RivenHexagon/TAC_Scorpion/AML_LineIn/LineInMod.pdf

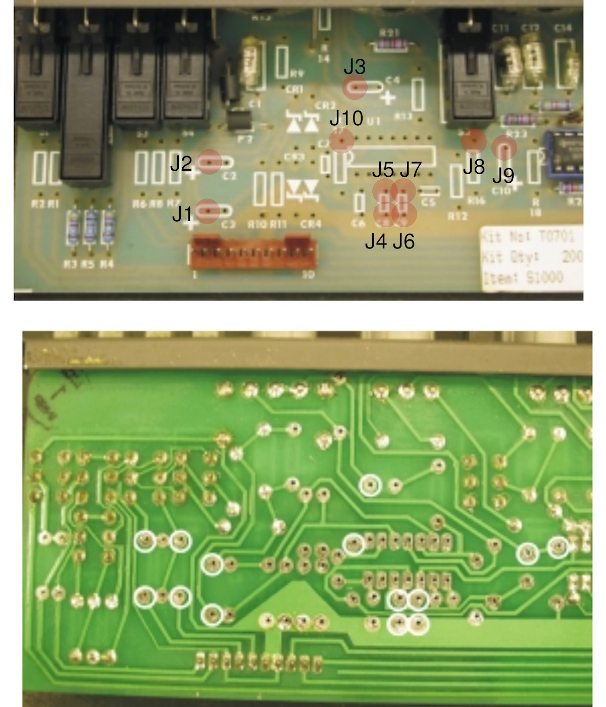
[picture p6: figure]
