RivenHexagon/TAC_Scorpion/AML_MicIn/MicInMod.pdf

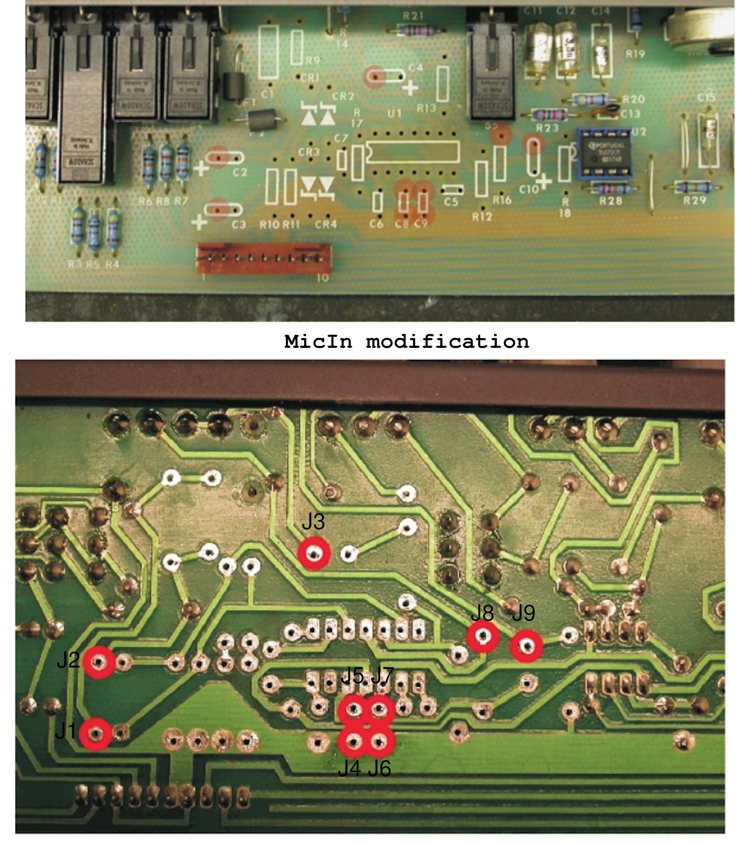
[picture p7: figure]
