RivenHexagon/TAC_Scorpion/AML_LineIn/AML-LineIn.jpg

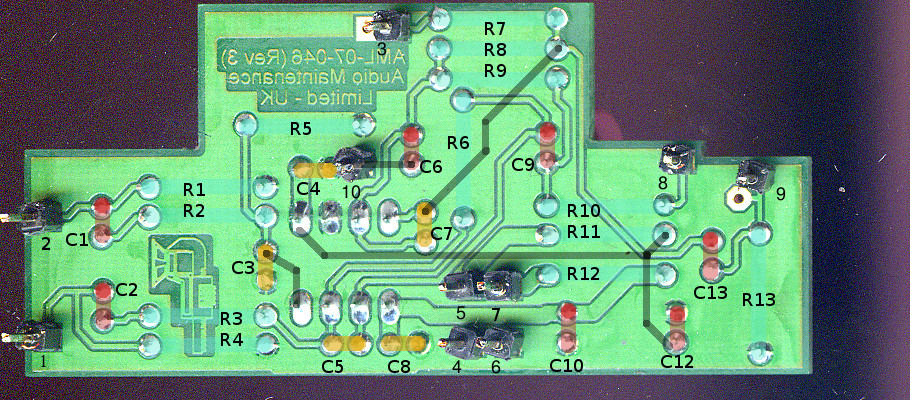
AML_LineIn/AML-LineIn.jpg
