RivenHexagon/TAC_Scorpion/DOA_SK25RHX/Docs/194913907.jpg

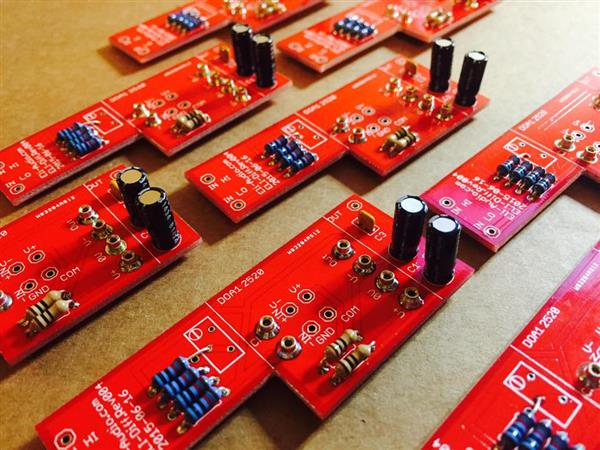
DOA_SK25RHX/Docs/194913907.jpg
