RivenHexagon/TAC_Scorpion/DOA_SK25RHX/Docs/194914601.jpg

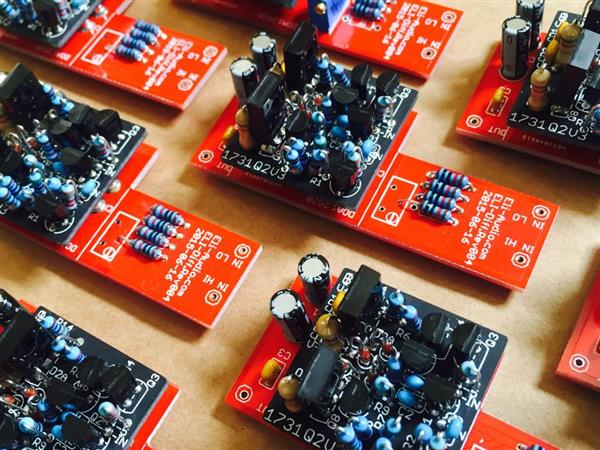
DOA_SK25RHX/Docs/194914601.jpg
