RivenHexagon/TAC_Scorpion/DOA_SK25RHX/Docs/194915174.jpg

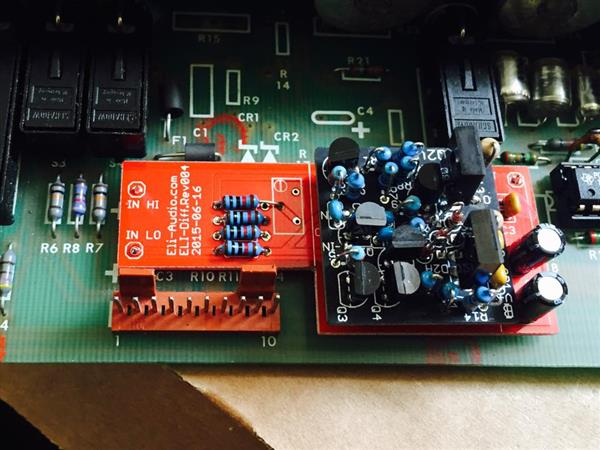
DOA_SK25RHX/Docs/194915174.jpg
