RivenHexagon/TAC_Scorpion/TAC_GL270D/GL270-DOA2520.kicad_pro/PCB_GL270D-flip.jpg

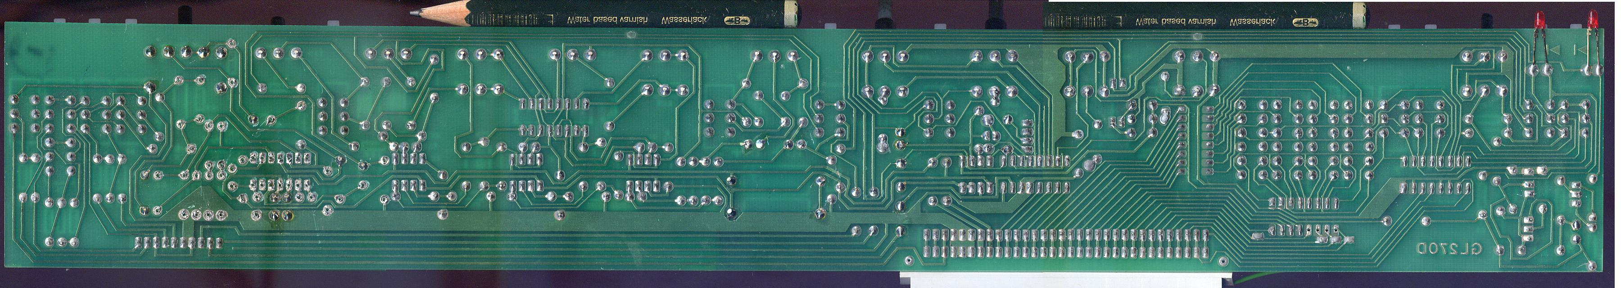
TAC_GL270D/GL270-DOA2520.kicad_pro/PCB_GL270D-flip.jpg
