RivenHexagon/TAC_Scorpion/DOA_SK25RHX/SK25.pdf

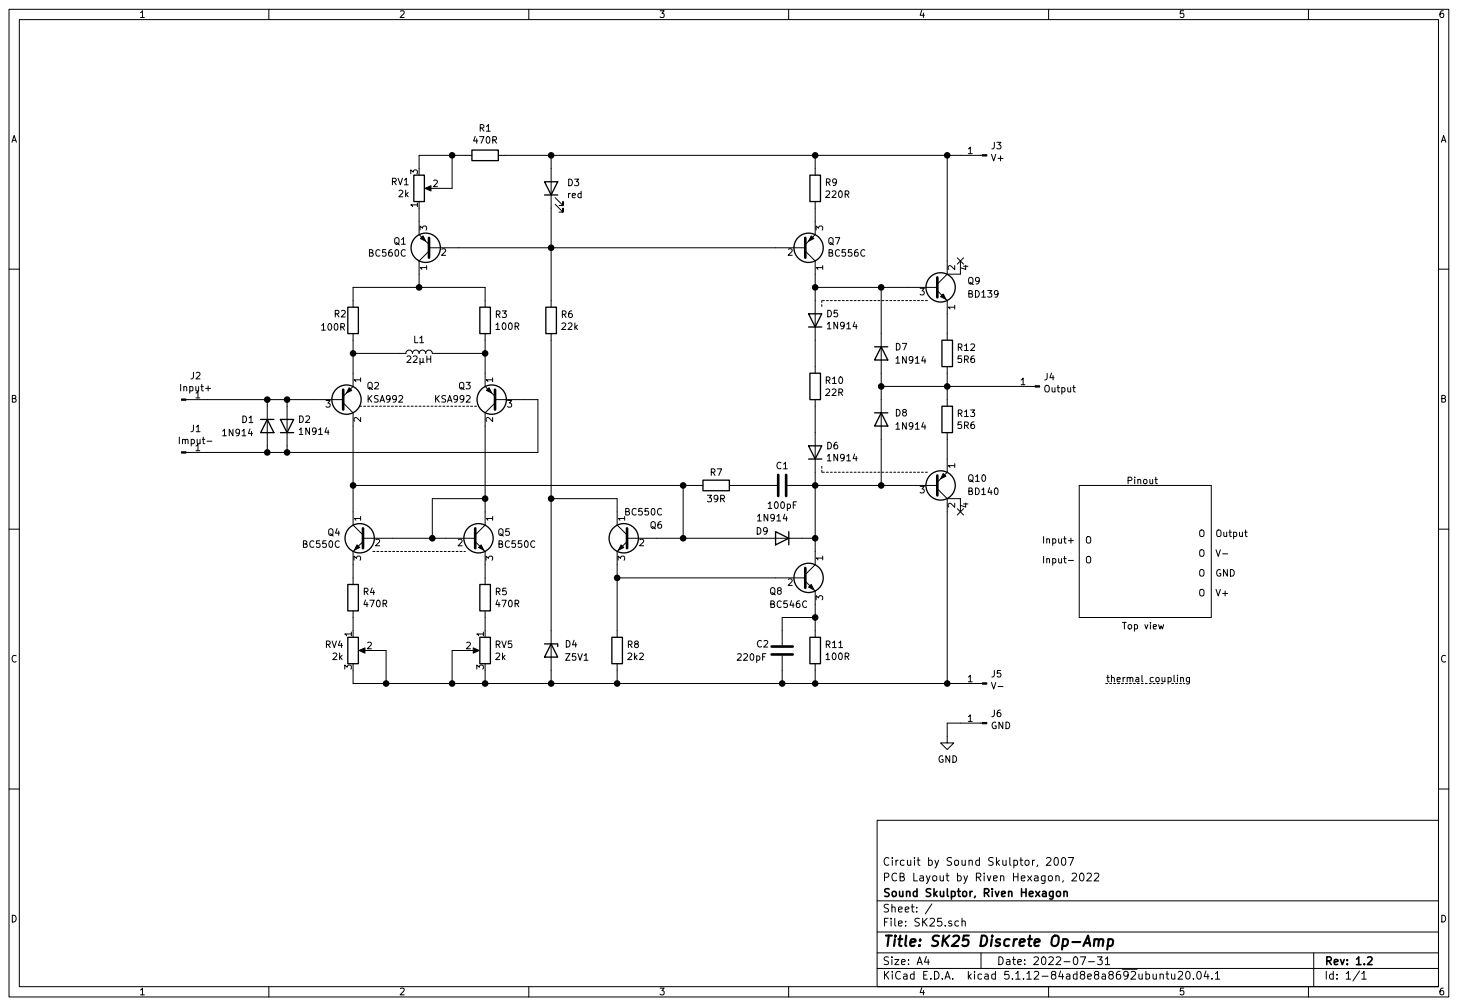
[picture p64: page 1]

Circuit by Sound Skulptor, 2007 D6

PCB Layout by Riven Hexagon, 2022
File: SK25.sch Sheet: / Sound Skulptor, Riven Hexagon

Id: 1/1 Title: SK25 Discrete Op-Amp
