RivenHexagon/TAC_Scorpion/TAC_GL270D/GL270-LineIn.pdf

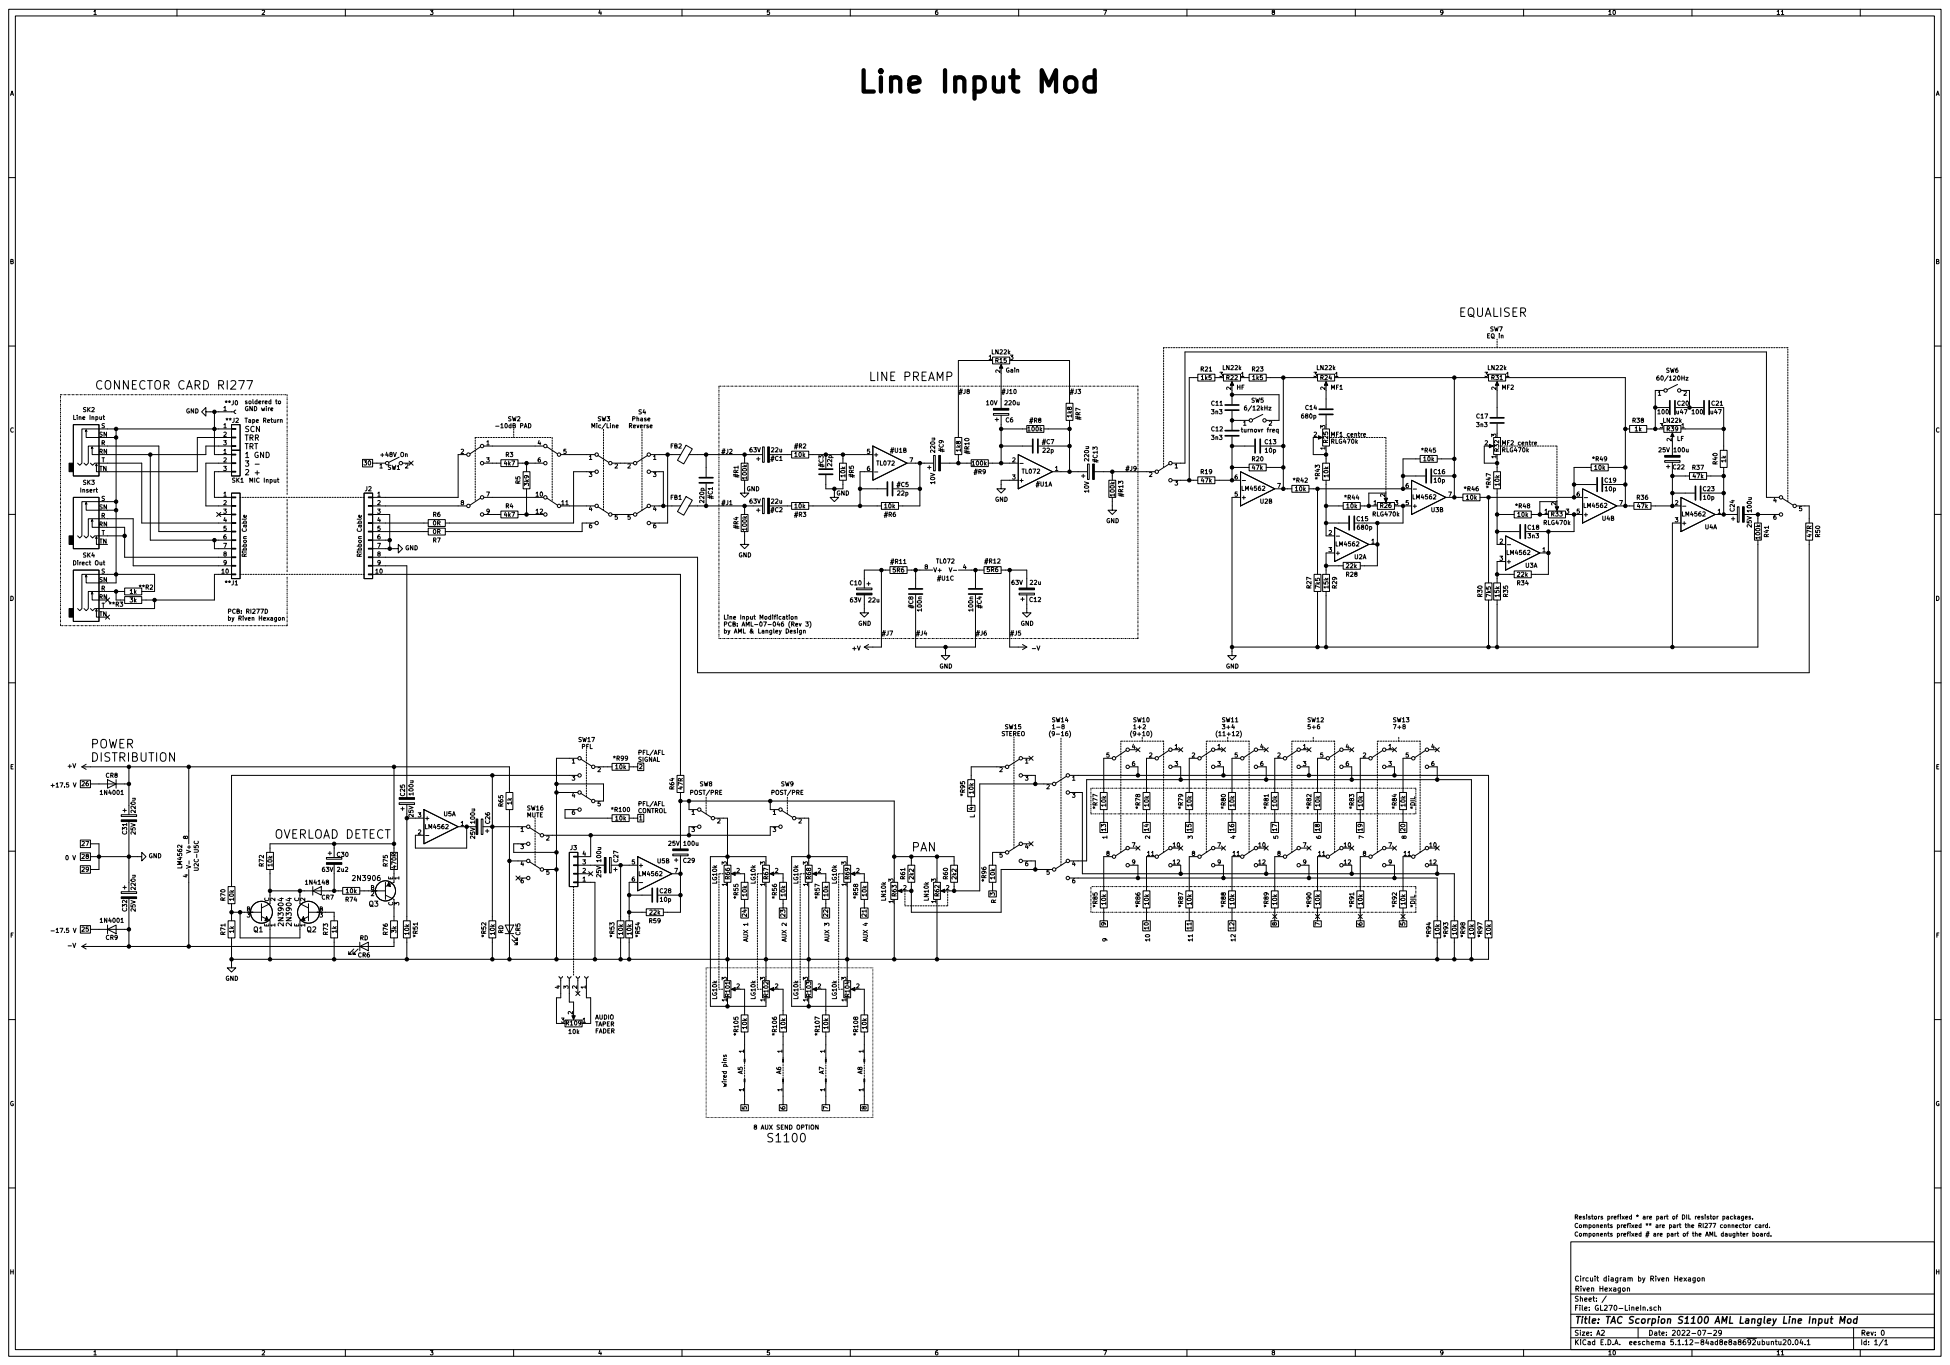
[picture p65: page 1]

Components prefixed ** are part the RI277 connector card. AUX 2

Resistors prefixed * are part of DIL resistor packages.

Circuit diagram by Riven Hexagon
File: GL270-LineIn.sch Sheet: / Riven Hexagon

Id: 1/1 Title: TAC Scorpion S1100 AML Langley Line Input Mod
