RivenHexagon/TAC_Scorpion/TAC_GL270D/GL270-MicIn.pdf

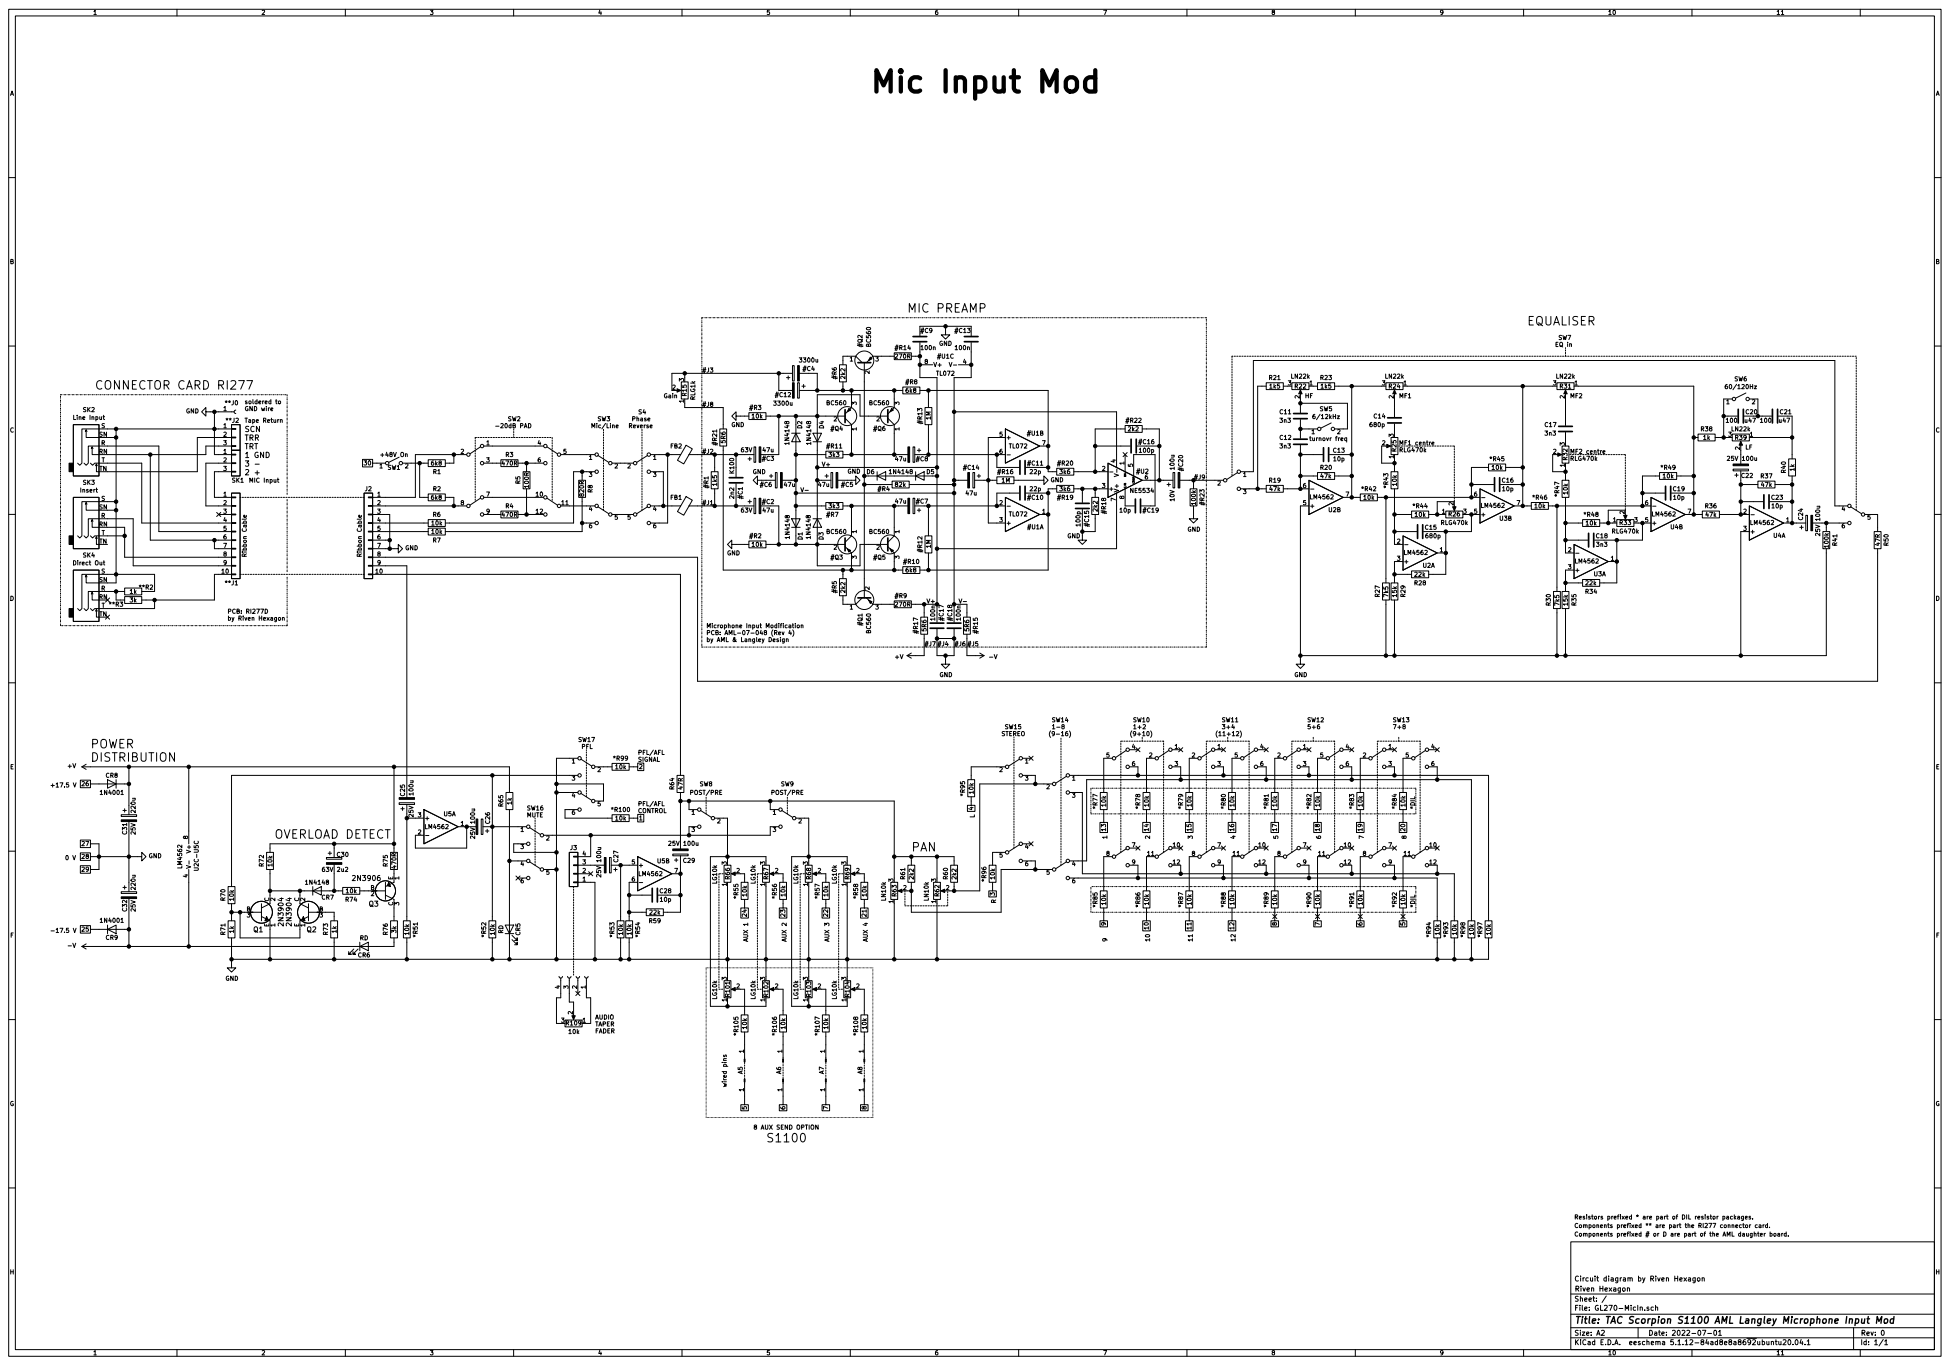
[picture p66: page 1]

soldered to GND wire +V

by AML & Langley Design AUX 2

Resistors prefixed * are part of DIL resistor packages.
Components prefixed ** are part the RI277 connector card.
Components prefixed # or D are part of the AML daughter board.

Circuit diagram by Riven Hexagon
File: GL270-MicIn.sch Sheet: / Riven Hexagon

Id: 1/1 Title: TAC Scorpion S1100 AML Langley Microphone Input Mod
