RivenHexagon/TAC_Scorpion/AML_LineIn/AML-07-046.pdf

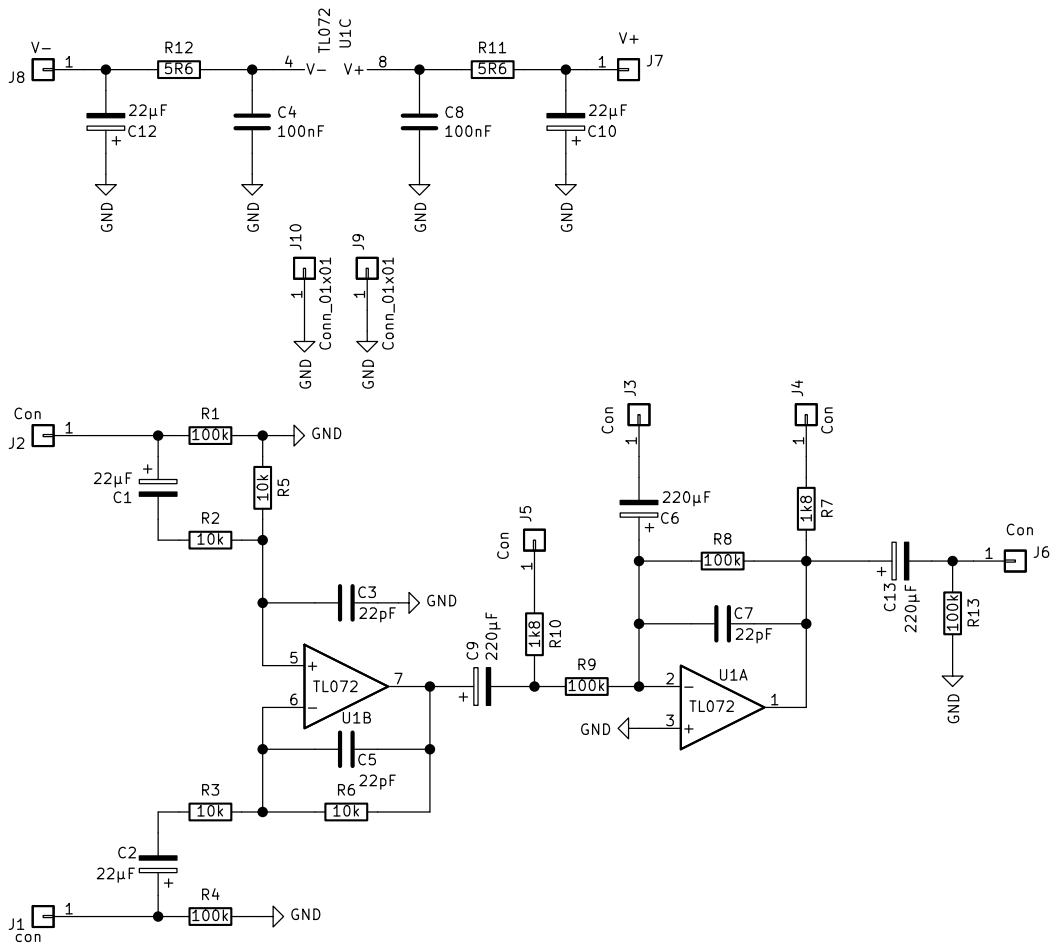
[picture p72: page 1]

Id: 1/1 Title: Scorpion Line Input File: AML-07-046.sch Sheet: /
