RivenHexagon/TAC_Scorpion/TAC_JP280/JP280C-B_Cu.pdf

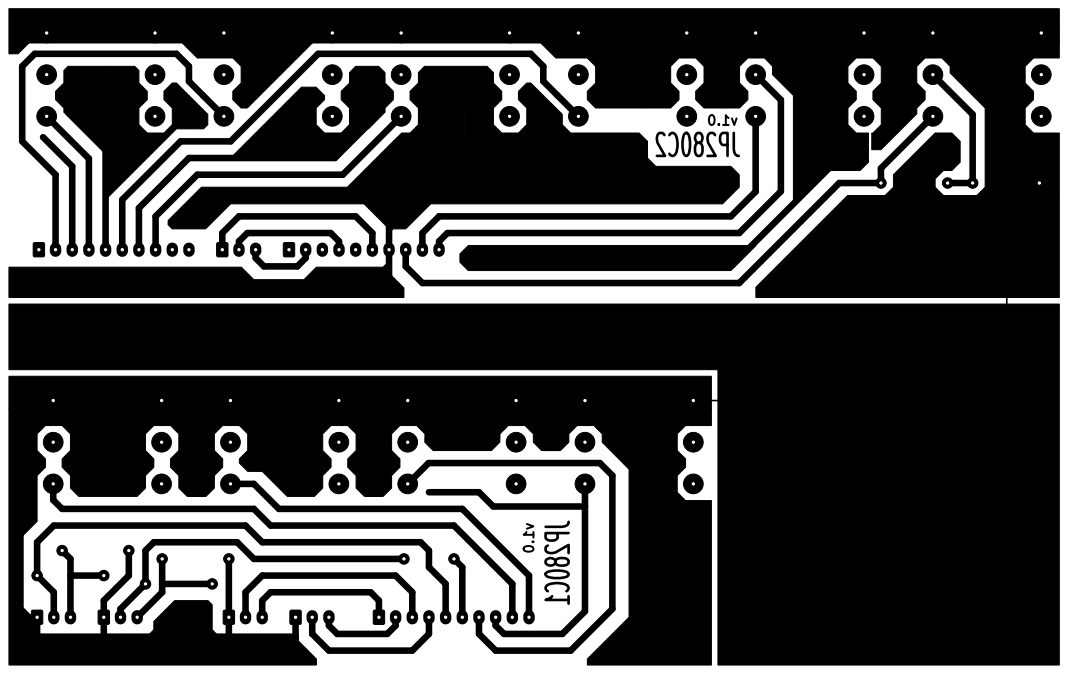
[picture p73: page 1]
