RivenHexagon/TAC_Scorpion/TAC_RI277/RI277D_v1.2.pdf

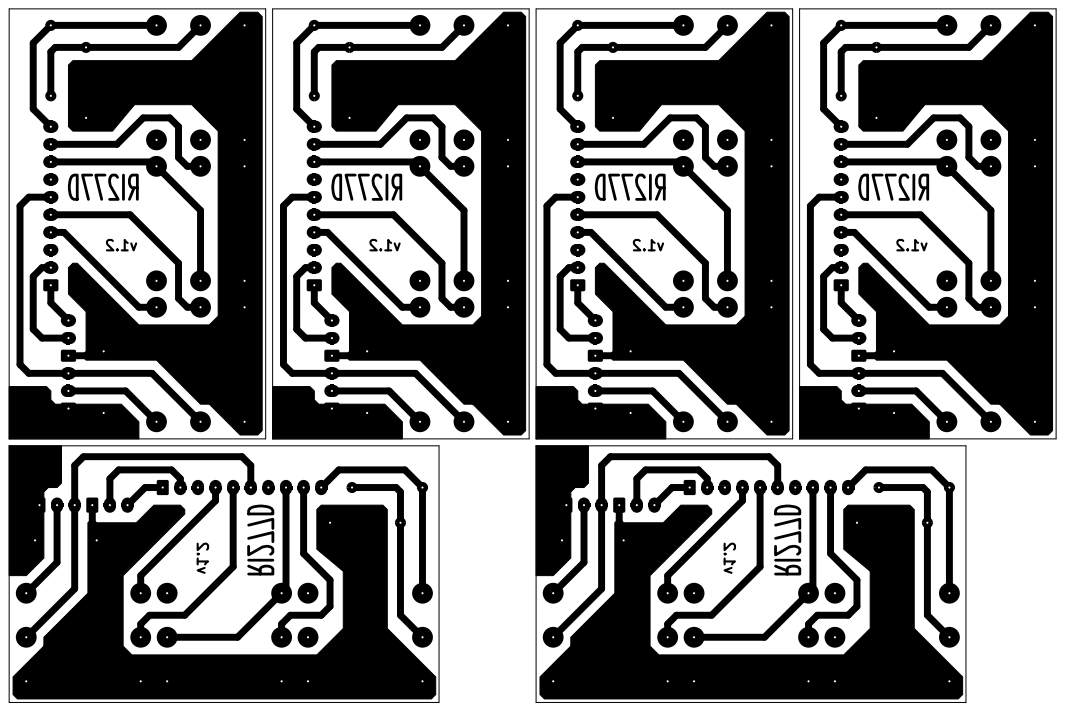
[picture p74: page 1]
