RivenHexagon/TAC_Scorpion/TAC_RI279/RI279C_v1.0.pdf

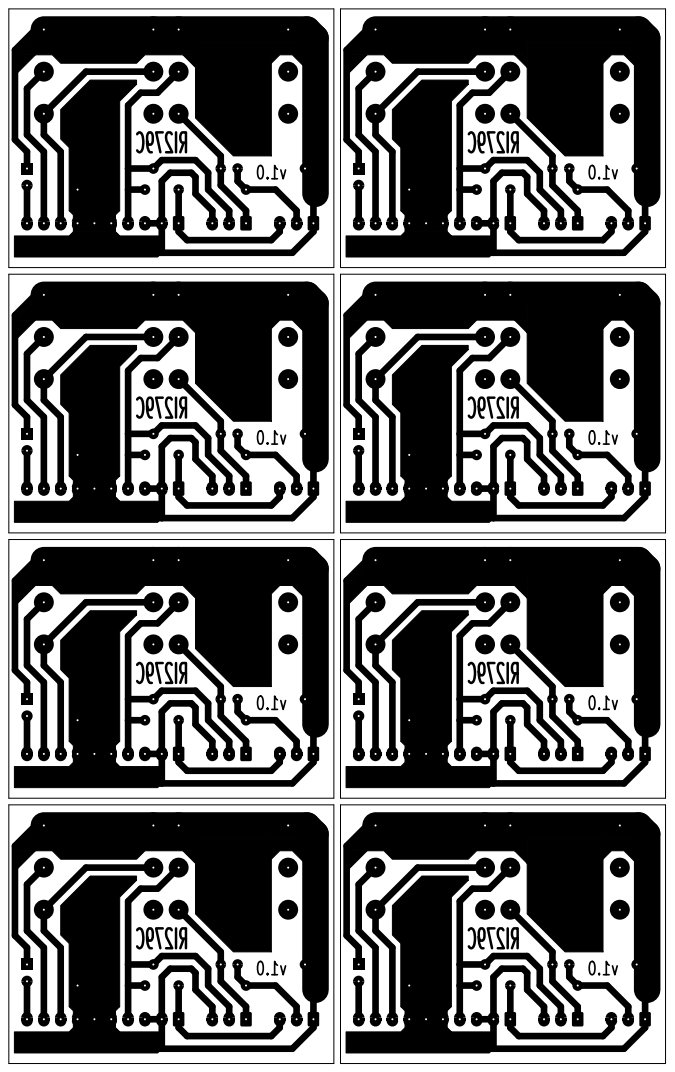
[picture p75: page 1]
