RivenHexagon/TAC_Scorpion/DOA_SK25RHX/Docs/sk25-layout-03.pdf

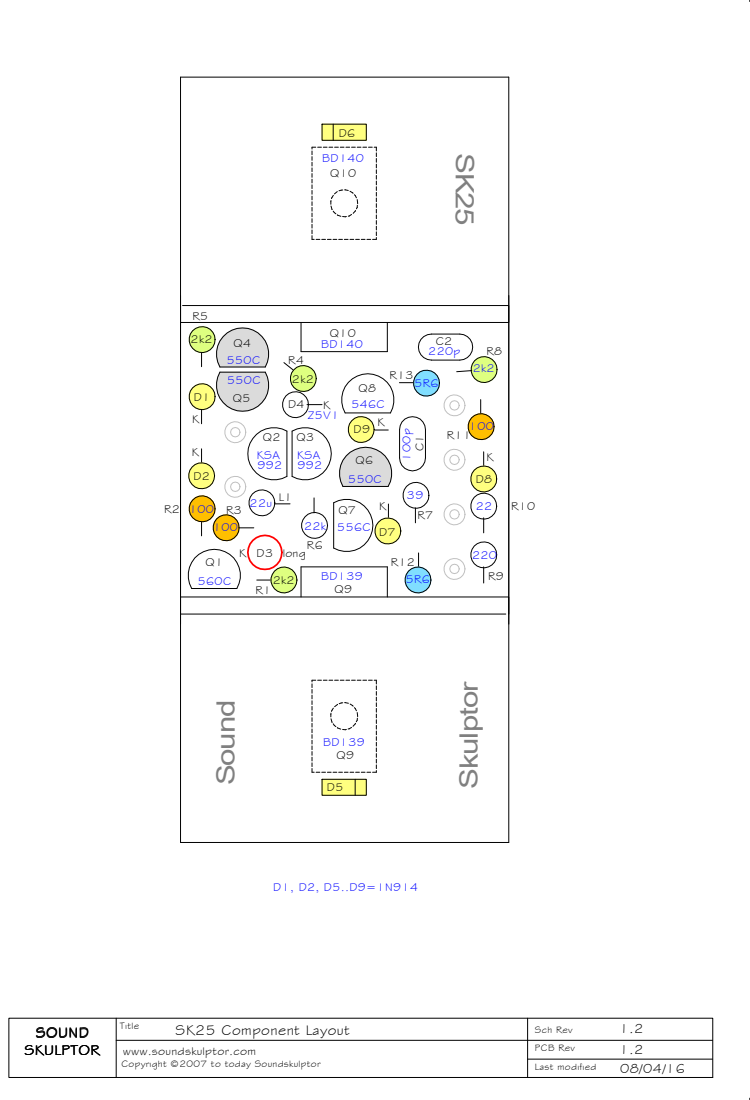
[picture p76: page 1]

www.soundskulptor.com
Copyright ©2007 to today Soundskulptor
