RivenHexagon/TAC_Scorpion/TAC_GL270D/GL270-DOA2520.kicad_pro/GL270-DOA2520.kicad_pro.kicad_sch

## KiCad design TAC_GL270D/GL270-DOA2520.kicad_pro/GL270-DOA2520.kicad_pro.kicad_sch (2023-12-30)

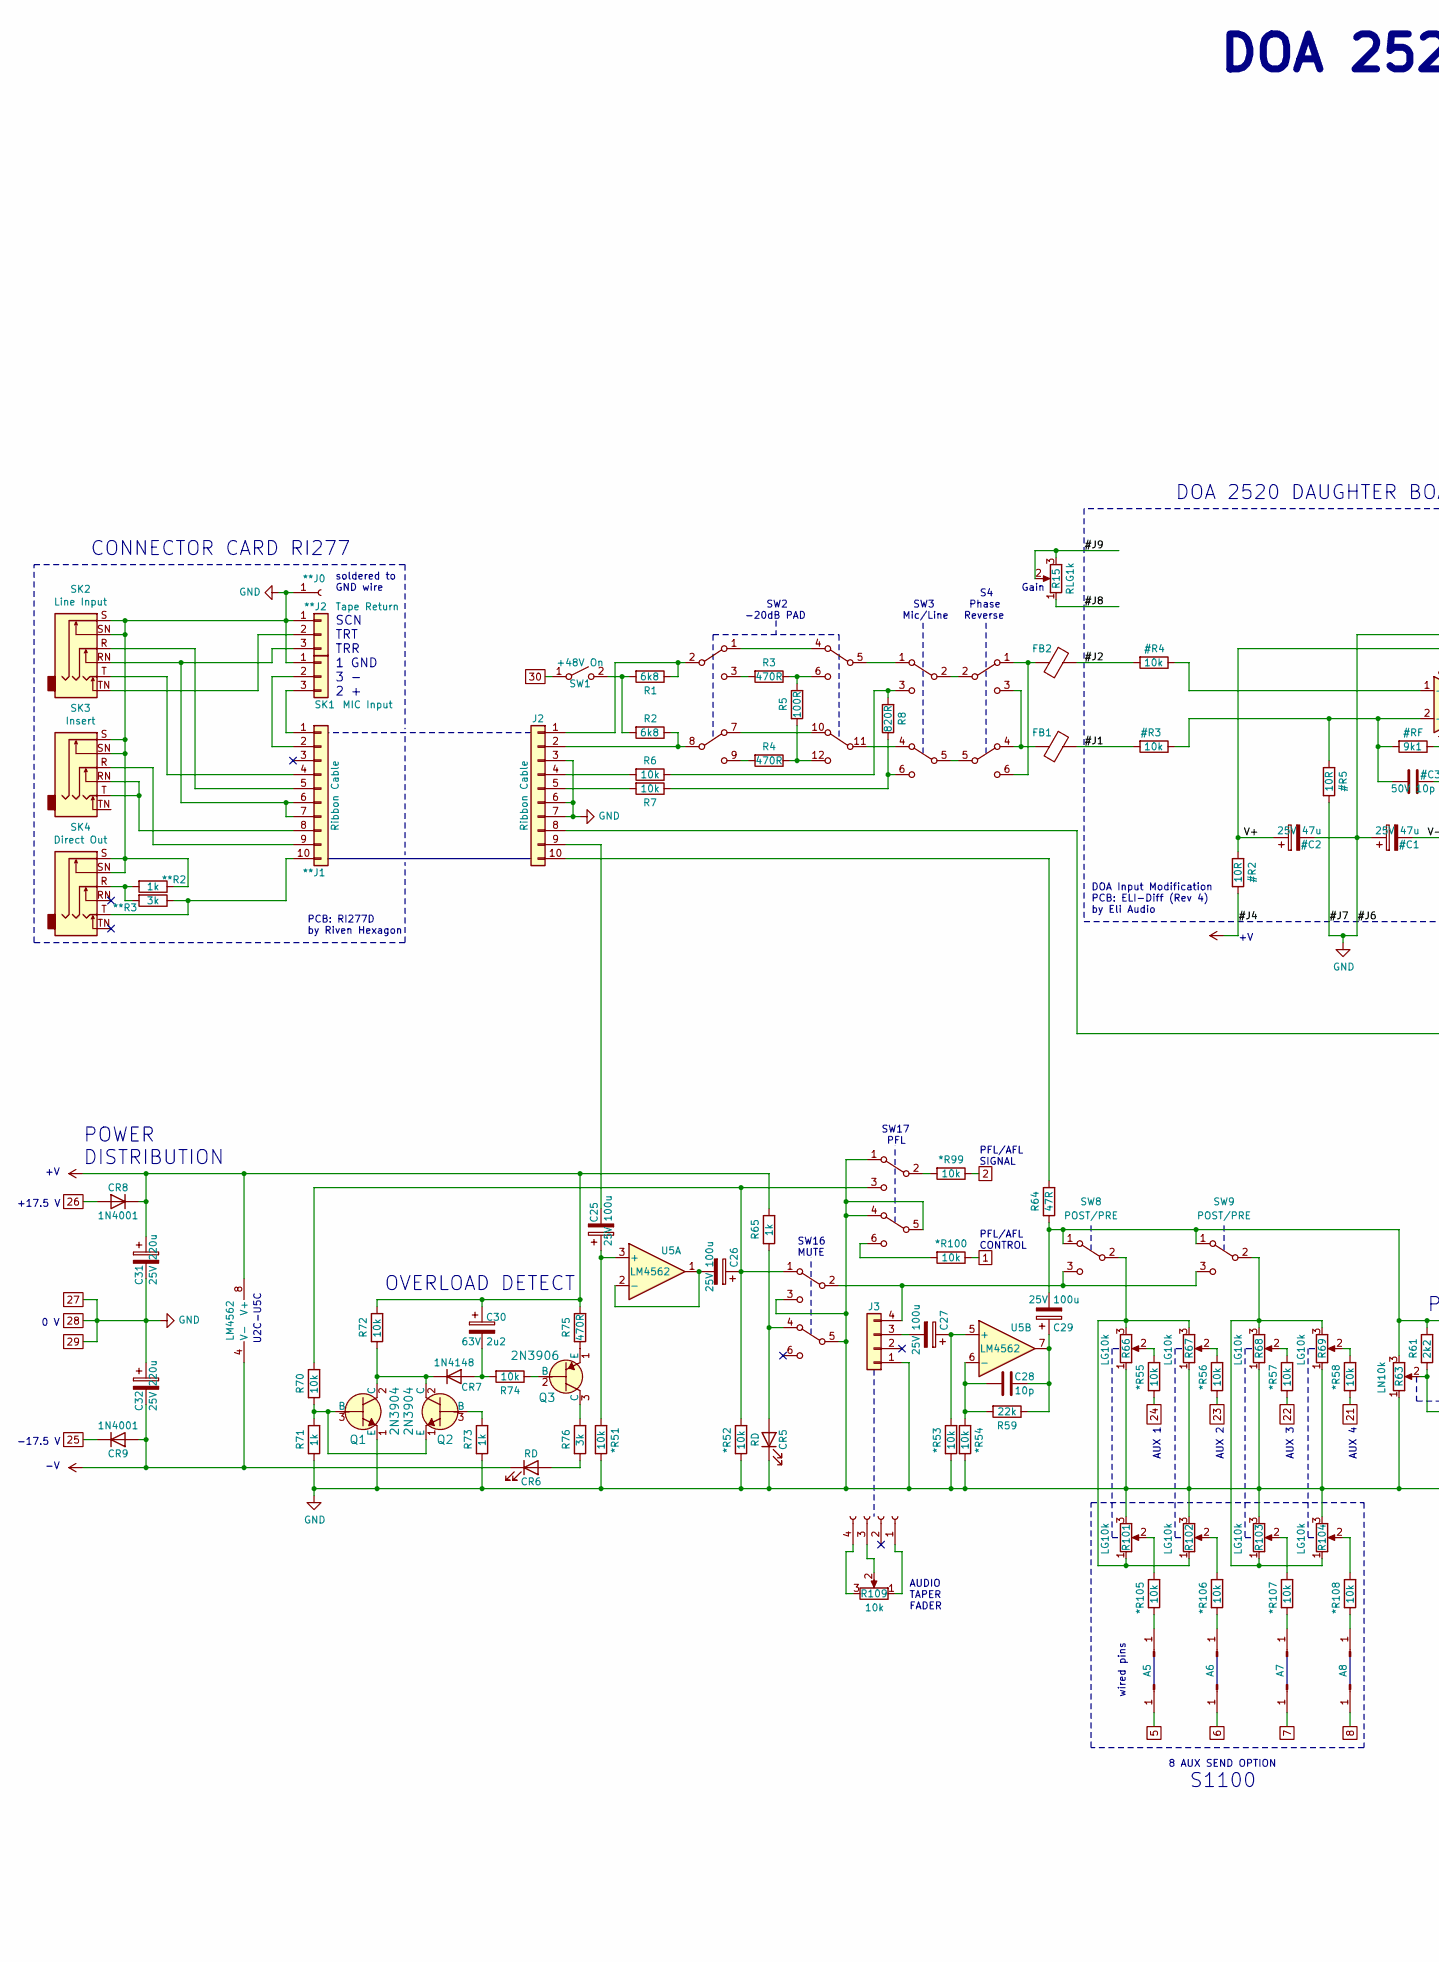
[picture p85: schematic GL270-DOA2520.kicad_pro.kicad_sch, part in row 1, column 1]

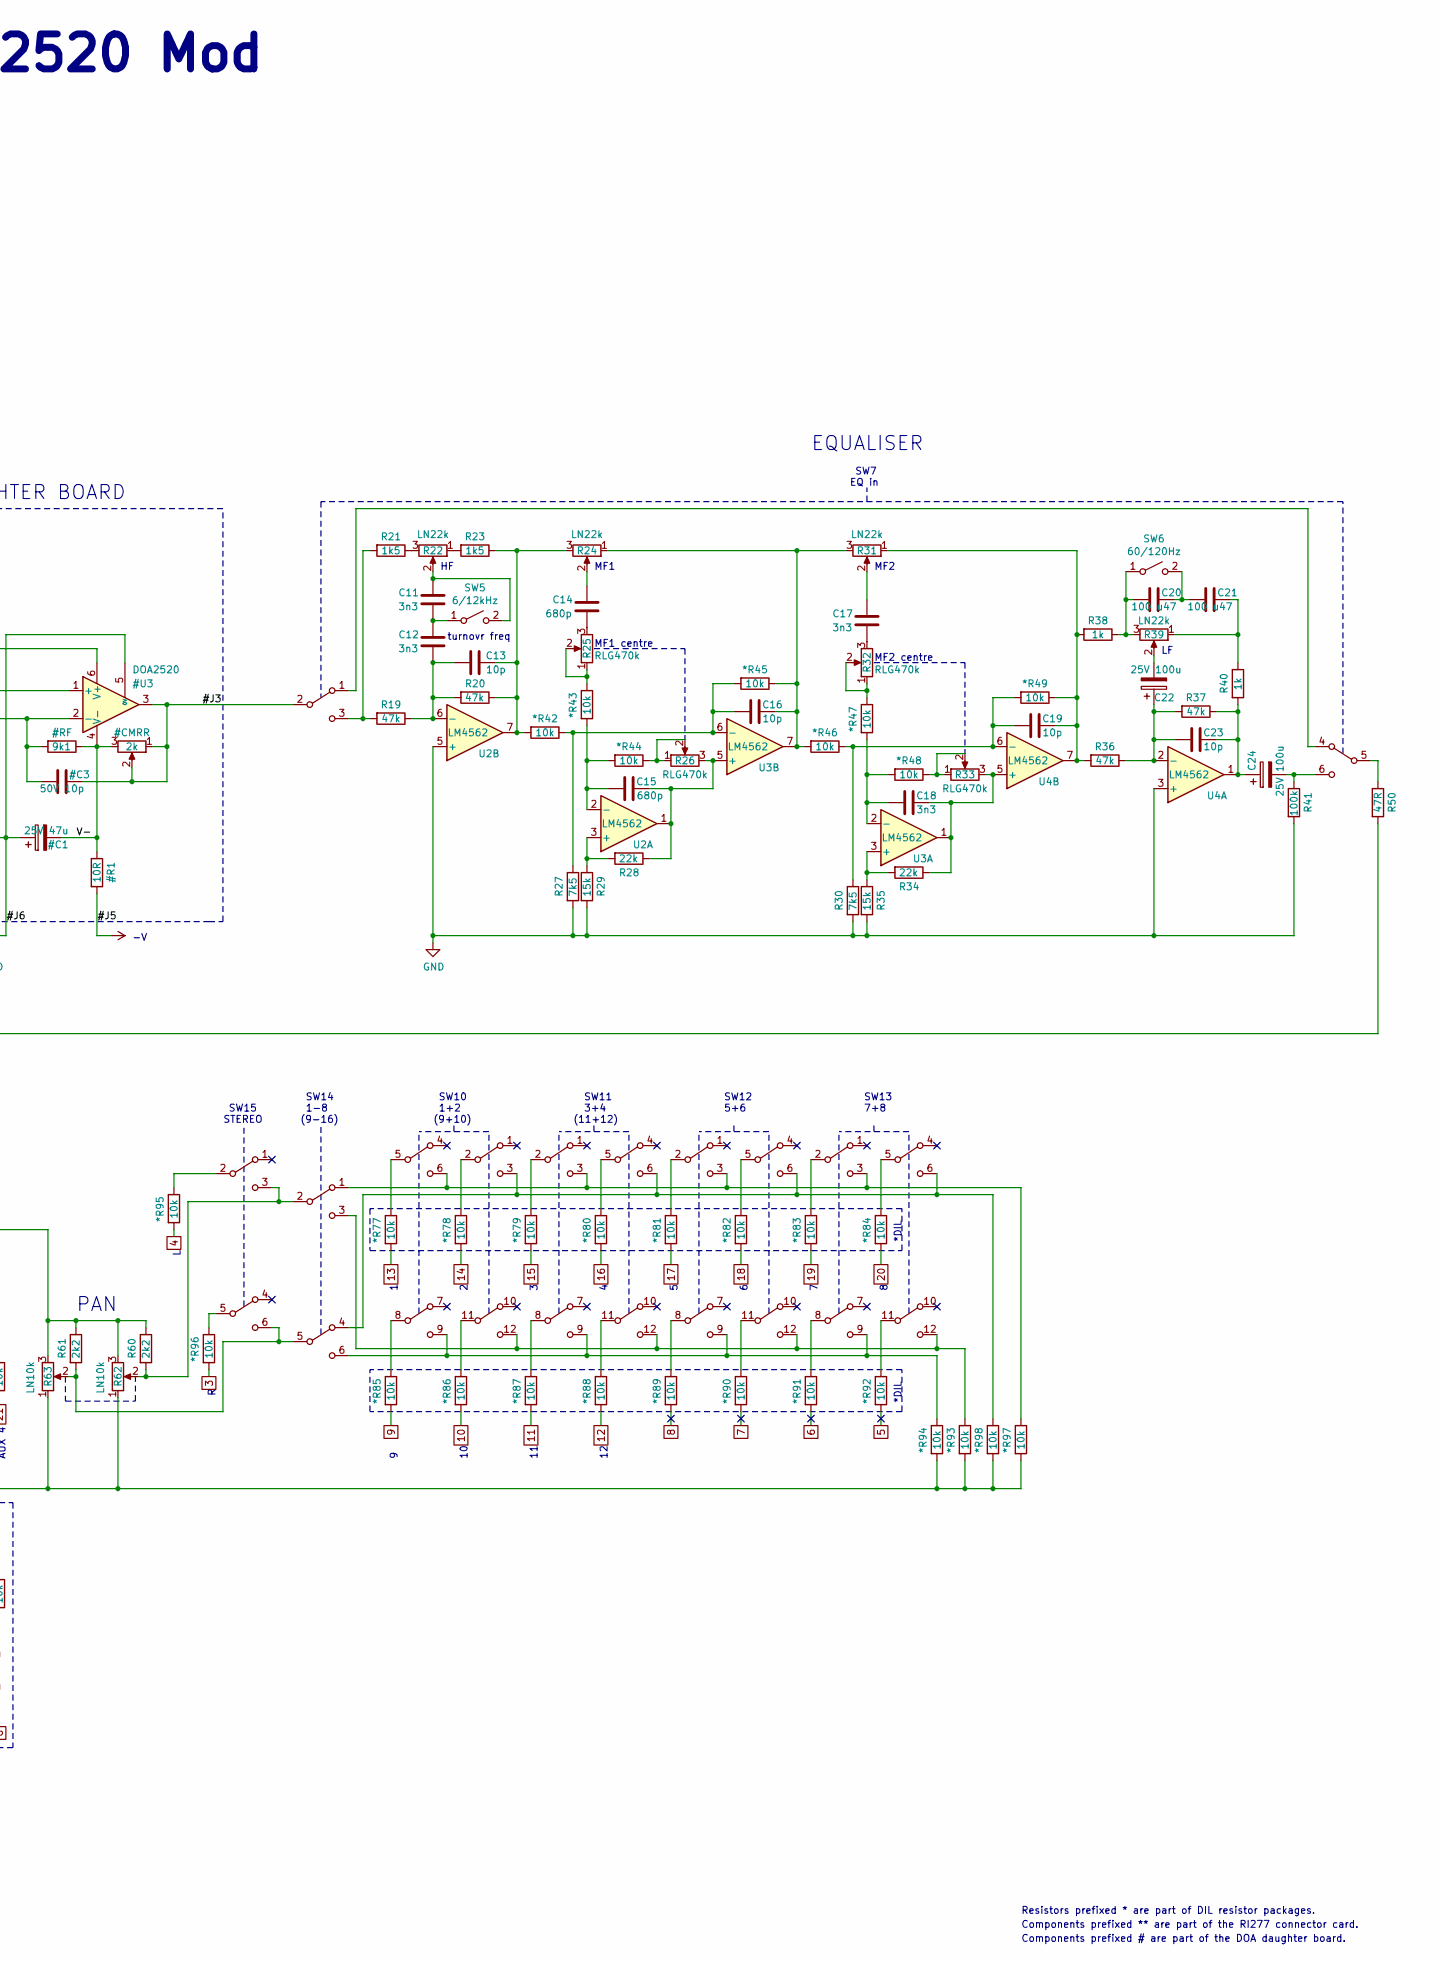
[picture p86: schematic GL270-DOA2520.kicad_pro.kicad_sch, part in row 1, column 2]

Parts:
**J0: to GND wire
**J1: Ribbon Cable
**J2: Tape Return
**R2: 1k
**R3: 3k
*R42, *R43, *R44, *R45, *R46, *R47, *R48, *R49, *R51, *R52, *R53, *R54, *R55, *R56, *R57, *R58, *R77, *R78, *R79, *R80, *R81, *R82, *R83, *R84, *R85, *R86, *R87, *R88, *R89, *R90, *R91, *R92, *R93, *R94, *R95, *R96, *R97, *R98, *R99, *R100, *R105, *R106, *R107, *R108: 10k
A5, A6, A7, A8: Conn_01x01_Male
B5, B6, B7, B8: Conn_01x01_Male
C11, C12, C17, C18: 3n3
C13, C16, C19, C23, C28: 10p
C14, C15: 680p
C20, C21: 100 u47
C22, C24, C25, C26, C27, C29: 25V 100u
C30: 63V 2u2
C31, C32: 25V 220u
CR5, CR6: RD
CR7: 1N4148
CR8, CR9: 1N4001
FB1, FB2: Ferrite_Bead
J2: Ribbon Cable
J3: (10k)
Q1, Q2: 2N3904; TO-92-3; MPN 2N3904; Digi-Key_PN 2N3904CS-ND
Q3: 2N3906; TO-92-3; MPN 2N3906; Digi-Key_PN 2N3906CS-ND
R1, R2: 6k8
R3, R4, R75: 470R
R5: 100R
R6, R7, R70, R72, R74, R109: 10k
R8: 820R
R15: RLG1k
R19, R20, R36, R37: 47k
R21, R23: 1k5
R22, R24, R31, R39: LN22k
R25, R26, R32, R33: RLG470k
R27, R30: 7k5
R28, R34, R59: 22k
R29, R35: 15k
R38, R40, R65, R71, R73: 1k
R41: 100k
R50, R64: 47R
R60, R61: 2k2
R62, R63: LN10k
R66, R67, R68, R69, R101, R102, R103, R104: LG10k
R76: 3k
SK1: MIC Input
SK2: Line Input
SK3: Insert
SK4: Direct Out
SW1: +48V On
SW2, SW10, SW11, SW12, SW13: SW_QPDT_x4
SW3, SW4, SW7, SW14, SW15, SW16, SW17: SW_DPDT_x2
SW5: 6/12kHz
SW6: 60/120Hz
SW8, SW9: POST/PRE
U2, U3, U4, U5: LM4562

Connections:
1: *R100.1
2: *R99.1
3: *R96.2
4: *R95.2
5: *R92.2, B5.1
6: *R91.2, B6.1
7: *R90.2, B7.1
8: *R89.2, B8.1
9: *R85.2
10: *R86.2
10k: *R51.2, *R52.2, *R53.2, *R54.2, *R93.2, *R94.2, *R97.2, *R98.2, C30.1, C31.1, C32.2, CR5.1 (K), CR6.1 (K), CR8.1 (K), CR9.2 (A), FB1.1, FB2.1, J2.3, J2.6, J2.7, J3.1, Q1.1 (E), R62.1, R63.1, R65.1, R66.1, R67.1, R68.1, R69.1, R71.2, R72.1, R73.2, R75.1, R101.3, R102.3, R103.3, R104.3, SW7.2 (B), SW16.3 (C), SW16.5 (B), SW17.1 (A), SW17.4 (A), SW17.5 (B)
11: *R87.2
12: *R88.2
13: *R77.2
14: *R78.2
15: *R79.2
16: *R80.2
17: *R81.2
18: *R82.2
19: *R83.2
20: *R84.2
21: *R58.2
22: *R57.2
23: *R56.2
24: *R55.2
25: CR9.1 (K)
26: CR8.2 (A)
27: C31.2, C32.1
30: SW1.1 (A)
#J8: R15.1
#J9: R15.2, R15.3
unnamed: **J0.1, **J2.1, **R2.1, SK1.1, SK2.S, SK2.SN, SK3.S, SK3.SN, SK4.S, SK4.SN
unnamed: **J1.1, SK1.3
unnamed: **J1.2, SK1.2
unnamed: **J1.4, SK2.T
unnamed: **J1.5, SK2.R
unnamed: **J1.6, **J1.7, **J2.3, SK2.RN
unnamed: **J1.8, SK3.RN, SK3.T
unnamed: **J1.9, SK3.R
unnamed: **J1.10, **R3.1, SK4.T
unnamed: **J2.2, SK2.TN
unnamed: **R2.2, **R3.2, SK4.R
unnamed: *R42.1, *R45.2, C16.2, R27.1, U3.6 (-)
unnamed: *R42.2, C13.1, R20.1, R23.1, R24.3, U2.7
unnamed: *R43.1, R25.1, R25.2
unnamed: *R43.2, *R44.2, C15.2, U2.2 (-)
unnamed: *R44.1, R26.1, R26.2
unnamed: *R45.1, *R46.2, C16.1, R24.1, R31.3, U3.7
unnamed: *R46.1, *R49.2, C19.2, R30.1, U4.6 (-)
unnamed: *R47.1, R32.1, R32.2
unnamed: *R47.2, *R48.2, C18.2, U3.2 (-)
unnamed: *R48.1, R33.1, R33.2
unnamed: *R49.1, C19.1, R31.1, R36.2, R38.2, U4.7
unnamed: *R51.1, C25.1, U5.3 (+)
unnamed: *R52.1, C26.1, R70.1, SW16.1 (A), SW17.3 (C)
unnamed: *R53.1, C27.1, U5.5 (+)
unnamed: *R54.1, C28.2, R59.2, U5.6 (-)
unnamed: *R55.1, R66.2
unnamed: *R56.1, R67.2
unnamed: *R57.1, R68.2
unnamed: *R58.1, R69.2
unnamed: *R77.1, SW10.5
unnamed: *R78.1, SW10.2
unnamed: *R79.1, SW11.2
unnamed: *R80.1, SW11.5
unnamed: *R81.1, SW12.2
unnamed: *R82.1, SW12.5
unnamed: *R83.1, SW13.2
unnamed: *R84.1, SW13.5
unnamed: *R85.1, SW10.8
unnamed: *R86.1, SW10.11
unnamed: *R87.1, SW11.8
unnamed: *R88.1, SW11.11
unnamed: *R89.1, SW12.8
unnamed: *R90.1, SW12.11
unnamed: *R91.1, SW13.8
unnamed: *R92.1, SW13.11
unnamed: *R93.1, SW10.12, SW11.12, SW12.12, SW13.12, SW14.3 (C)
unnamed: *R94.1, SW10.9, SW11.9, SW12.9, SW13.9, SW14.6 (C)
unnamed: *R95.1, SW15.2 (B)
unnamed: *R96.1, SW15.5 (B)
unnamed: *R97.1, SW10.6, SW11.3, SW12.3, SW13.3, SW14.1 (A)
unnamed: *R98.1, SW10.3, SW11.6, SW12.6, SW13.6, SW14.4 (A)
unnamed: *R99.2, SW17.2 (B)
unnamed: *R100.2, SW17.6 (C)
unnamed: *R105.1, R101.2
unnamed: *R105.2, A5.1
unnamed: *R106.1, R102.2
unnamed: *R106.2, A6.1
unnamed: *R107.1, R103.2
unnamed: *R107.2, A7.1
unnamed: *R108.1, R104.2
unnamed: *R108.2, A8.1
unnamed: C11.1, R22.2, SW5.2 (B)
unnamed: C11.2, C12.1, SW5.1 (A)
unnamed: C12.2, C13.2, R19.1, R20.2, U2.6 (-)
unnamed: C14.1, R24.2
unnamed: C14.2, R25.3
unnamed: C15.1, R26.3, R28.1, U2.1, U3.5 (+)
unnamed: C17.1, R31.2
unnamed: C17.2, R32.3
unnamed: C18.1, R33.3, R34.1, U3.1, U4.5 (+)
unnamed: C20.1, C21.2, SW6.2 (B)
unnamed: C20.2, R38.1, R39.3, SW6.1 (A)
unnamed: C21.1, R39.1, R40.1
unnamed: C22.1, C23.2, R36.1, R37.2, U4.2 (-)
unnamed: C22.2, R39.2
unnamed: C23.1, C24.1, R37.1, R40.2, U4.1
unnamed: C24.2, R41.1, SW7.6 (C)
unnamed: C25.2, J2.9
unnamed: C26.2, U5.1, U5.2 (-)
unnamed: C27.2, J3.3
unnamed: C28.1, C29.1, R59.1, U5.7
unnamed: C29.2, R60.1, R61.1, R62.3, R63.3, R64.2, SW8.1 (A), SW9.1 (A)
unnamed: C30.2, CR7.2 (A), R74.2
unnamed: CR5.2 (A), R65.2, SW16.4 (A)
unnamed: CR6.2 (A), R76.2
unnamed: CR7.1 (K), Q1.2 (C), Q2.2 (C), R72.2
unnamed: FB1.2, SW4.3 (C), SW4.4 (A)
unnamed: FB2.2, SW4.1 (A), SW4.6 (C)
unnamed: J2.1, R1.1, SW2.2
unnamed: J2.2, R2.1, SW2.8
unnamed: J2.4, R6.2
unnamed: J2.5, R7.2
unnamed: J2.8, R50.2
unnamed: J2.10, R64.1
unnamed: J3.4, SW8.3 (C), SW9.3 (C), SW16.2 (B)
unnamed: Q1.3 (B), Q2.1 (E), R70.2, R71.1
unnamed: Q2.3 (B), R73.1
unnamed: Q3.1 (E), R75.2
unnamed: Q3.2 (B), R74.1
unnamed: Q3.3 (C), R76.1
unnamed: R1.2, R2.2, SW1.2 (B)
unnamed: R3.1, R5.1, SW2.6
unnamed: R3.2, SW2.3
unnamed: R4.1, R5.2, SW2.12
unnamed: R4.2, SW2.9
unnamed: R6.1, R8.2, SW3.3 (C)
unnamed: R7.1, R8.1, SW3.6 (C)
unnamed: R19.2, R21.2, SW7.3 (C)
unnamed: R21.1, R22.3
unnamed: R22.1, R23.2
unnamed: R27.2, R29.2, R30.2, R35.2, R41.2, U2.5 (+), U4.3 (+)
unnamed: R28.2, R29.1, U2.3 (+)
unnamed: R34.2, R35.1, U3.3 (+)
unnamed: R50.1, SW7.5 (B)
unnamed: R60.2, R62.2, SW14.2 (B), SW15.3 (C)
unnamed: R61.2, R63.2, SW14.5 (B), SW15.6 (C)
unnamed: R66.3, R67.3, R101.1, R102.1, SW8.2 (B)
unnamed: R68.3, R69.3, R103.1, R104.1, SW9.2 (B)
unnamed: SW2.1, SW2.4
unnamed: SW2.5, SW3.1 (A)
unnamed: SW2.7, SW2.10
unnamed: SW2.11, SW3.4 (A)
unnamed: SW3.2 (B), SW4.2 (B)
unnamed: SW3.5 (B), SW4.5 (B)
unnamed: SW7.1 (A), SW7.4 (A)

Notes on the sheet:
SW11 3+4 (11+12)
PCB: RI277D by Riven Hexagon
turnovr freq
SW14 1-8 (9-16)
SW17 PFL
AUX 4
PFL/AFL SIGNAL
soldered to GND wire
SW13 7+8
MF2
PFL/AFL CONTROL
AUX 3
0 V
8 AUX SEND OPTION
*DIL
AUX 2
DOA 2520 Mod
AUDIO TAPER FADER
SW16 MUTE
+17.5 V
Resistors prefixed * are part of DIL resistor packages.
MF2 centre
SW12 5+6
PAN
SCN TRT TRR 1 GND 3 - 2 +
OVERLOAD DETECT
MF1 centre
wired pins
-17.5 V
CONNECTOR CARD RI277
U2C-U5C
Components prefixed ** are part of the RI277 connector card.
SW15 STEREO
SW7 EQ in
S1100
SW2 -20dB PAD
Components prefixed # are part of the DOA daughter board.
Gain
EQUALISER
S4 Phase Reverse
AUX 1
DOA 2520 DAUGHTER BOARD
SW10 1+2 (9+10)
SW3 Mic/Line
MF1
DOA Input Modification PCB: ELI-Diff (Rev 4) by Eli Audio
POWER DISTRIBUTION
